AGalfra/ucos-II/scr/Micrium/Template/OS2/os_cfg.h

/*
*********************************************************************************************************
*                                                uC/OS-II
*                                          The Real-Time Kernel
*
*                         (c) Copyright 1992-2019; Silicon Laboratories Inc.,
*                                400 W. Cesar Chavez, Austin, TX 78701
*
*                   All rights reserved. Protected by international copyright laws.
*
*                  Your use of this software is subject to your acceptance of the terms
*                  of a Silicon Labs Micrium software license, which can be obtained by
*                  contacting info@micrium.com. If you do not agree to the terms of this
*                  license, you may not use this software.
*
*                  Please help us continue to provide the Embedded community with the finest
*                  software available. Your honesty is greatly appreciated.
*
*                    You can find our product's documentation at: doc.micrium.com
*
*                          For more information visit us at: www.micrium.com
*********************************************************************************************************
*/

/*
*********************************************************************************************************
*
*                                 uC/OS-II Configuration File for V2.9x
*
* Filename : os_cfg.h
* Version  : V2.92.16
*********************************************************************************************************
*/

#ifndef OS_CFG_H
#define OS_CFG_H


                                       /* ---------------------- MISCELLANEOUS ----------------------- */
#define OS_APP_HOOKS_EN           1u   /* Application-defined hooks are called from the uC/OS-II hooks */
#define OS_ARG_CHK_EN             1u   /* Enable (1) or Disable (0) argument checking                  */
#define OS_CPU_HOOKS_EN           1u   /* uC/OS-II hooks are found in the processor port files         */

#define OS_DEBUG_EN               0u   /* Enable(1) debug variables                                    */

#define OS_EVENT_MULTI_EN         1u   /* Include code for OSEventPendMulti()                          */
#define OS_EVENT_NAME_EN          1u   /* Enable names for Sem, Mutex, Mbox and Q                      */

#define OS_LOWEST_PRIO           63u   /* Defines the lowest priority that can be assigned ...         */
                                       /* ... MUST NEVER be higher than 254!                           */

#define OS_MAX_EVENTS            12u   /* Max. number of event control blocks in your application      */
#define OS_MAX_FLAGS              5u   /* Max. number of Event Flag Groups    in your application      */
#define OS_MAX_MEM_PART           5u   /* Max. number of memory partitions                             */
#define OS_MAX_QS                 4u   /* Max. number of queue control blocks in your application      */
#define OS_MAX_TASKS             20u   /* Max. number of tasks in your application, MUST be >= 2       */

#define OS_SCHED_LOCK_EN          1u   /* Include code for OSSchedLock() and OSSchedUnlock()           */

#define OS_TICK_STEP_EN           1u   /* Enable tick stepping feature for uC/OS-View                  */
#define OS_TICKS_PER_SEC       1000u   /* Set the number of ticks in one second                        */

#define OS_TLS_TBL_SIZE           0u   /* Size of Thread-Local Storage Table                           */


                                       /* --------------------- TASK STACK SIZE ---------------------- */
#define OS_TASK_TMR_STK_SIZE    128u   /* Timer      task stack size (# of OS_STK wide entries)        */
#define OS_TASK_STAT_STK_SIZE   128u   /* Statistics task stack size (# of OS_STK wide entries)        */
#define OS_TASK_IDLE_STK_SIZE   128u   /* Idle       task stack size (# of OS_STK wide entries)        */


                                       /* --------------------- TASK MANAGEMENT ---------------------- */
#define OS_TASK_CHANGE_PRIO_EN    1u   /*     Include code for OSTaskChangePrio()                      */
#define OS_TASK_CREATE_EN         1u   /*     Include code for OSTaskCreate()                          */
#define OS_TASK_CREATE_EXT_EN     1u   /*     Include code for OSTaskCreateExt()                       */
#define OS_TASK_DEL_EN            1u   /*     Include code for OSTaskDel()                             */
#define OS_TASK_NAME_EN           1u   /*     Enable task names                                        */
#define OS_TASK_PROFILE_EN        1u   /*     Include variables in OS_TCB for profiling                */
#define OS_TASK_QUERY_EN          1u   /*     Include code for OSTaskQuery()                           */
#define OS_TASK_REG_TBL_SIZE      1u   /*     Size of task variables array (#of INT32U entries)        */
#define OS_TASK_STAT_EN           1u   /*     Enable (1) or Disable(0) the statistics task             */
#define OS_TASK_STAT_STK_CHK_EN   1u   /*     Check task stacks from statistic task                    */
#define OS_TASK_SUSPEND_EN        1u   /*     Include code for OSTaskSuspend() and OSTaskResume()      */
#define OS_TASK_SW_HOOK_EN        1u   /*     Include code for OSTaskSwHook()                          */


                                       /* ----------------------- EVENT FLAGS ------------------------ */
#define OS_FLAG_EN                1u   /* Enable (1) or Disable (0) code generation for EVENT FLAGS    */
#define OS_FLAG_ACCEPT_EN         1u   /*     Include code for OSFlagAccept()                          */
#define OS_FLAG_DEL_EN            1u   /*     Include code for OSFlagDel()                             */
#define OS_FLAG_NAME_EN           1u   /*     Enable names for event flag group                        */
#define OS_FLAG_QUERY_EN          1u   /*     Include code for OSFlagQuery()                           */
#define OS_FLAG_WAIT_CLR_EN       1u   /* Include code for Wait on Clear EVENT FLAGS                   */
#define OS_FLAGS_NBITS           16u   /* Size in #bits of OS_FLAGS data type (8, 16 or 32)            */


                                       /* -------------------- MESSAGE MAILBOXES --------------------- */
#define OS_MBOX_EN                1u   /* Enable (1) or Disable (0) code generation for MAILBOXES      */
#define OS_MBOX_ACCEPT_EN         1u   /*     Include code for OSMboxAccept()                          */
#define OS_MBOX_DEL_EN            1u   /*     Include code for OSMboxDel()                             */
#define OS_MBOX_PEND_ABORT_EN     1u   /*     Include code for OSMboxPendAbort()                       */
#define OS_MBOX_POST_EN           1u   /*     Include code for OSMboxPost()                            */
#define OS_MBOX_POST_OPT_EN       1u   /*     Include code for OSMboxPostOpt()                         */
#define OS_MBOX_QUERY_EN          1u   /*     Include code for OSMboxQuery()                           */


                                       /* --------------------- MEMORY MANAGEMENT -------------------- */
#define OS_MEM_EN                 1u   /* Enable (1) or Disable (0) code generation for MEMORY MANAGER */
#define OS_MEM_NAME_EN            1u   /*     Enable memory partition names                            */
#define OS_MEM_QUERY_EN           1u   /*     Include code for OSMemQuery()                            */


                                       /* ---------------- MUTUAL EXCLUSION SEMAPHORES --------------- */
#define OS_MUTEX_EN               1u   /* Enable (1) or Disable (0) code generation for MUTEX          */
#define OS_MUTEX_ACCEPT_EN        1u   /*     Include code for OSMutexAccept()                         */
#define OS_MUTEX_DEL_EN           1u   /*     Include code for OSMutexDel()                            */
#define OS_MUTEX_QUERY_EN         1u   /*     Include code for OSMutexQuery()                          */


                                       /* ---------------------- MESSAGE QUEUES ---------------------- */
#define OS_Q_EN                   1u   /* Enable (1) or Disable (0) code generation for QUEUES         */
#define OS_Q_ACCEPT_EN            1u   /*     Include code for OSQAccept()                             */
#define OS_Q_DEL_EN               1u   /*     Include code for OSQDel()                                */
#define OS_Q_FLUSH_EN             1u   /*     Include code for OSQFlush()                              */
#define OS_Q_PEND_ABORT_EN        1u   /*     Include code for OSQPendAbort()                          */
#define OS_Q_POST_EN              1u   /*     Include code for OSQPost()                               */
#define OS_Q_POST_FRONT_EN        1u   /*     Include code for OSQPostFront()                          */
#define OS_Q_POST_OPT_EN          1u   /*     Include code for OSQPostOpt()                            */
#define OS_Q_QUERY_EN             1u   /*     Include code for OSQQuery()                              */


                                       /* ------------------------ SEMAPHORES ------------------------ */
#define OS_SEM_EN                 1u   /* Enable (1) or Disable (0) code generation for SEMAPHORES     */
#define OS_SEM_ACCEPT_EN          1u   /*    Include code for OSSemAccept()                            */
#define OS_SEM_DEL_EN             1u   /*    Include code for OSSemDel()                               */
#define OS_SEM_PEND_ABORT_EN      1u   /*    Include code for OSSemPendAbort()                         */
#define OS_SEM_QUERY_EN           1u   /*    Include code for OSSemQuery()                             */
#define OS_SEM_SET_EN             1u   /*    Include code for OSSemSet()                               */


                                       /* --------------------- TIME MANAGEMENT ---------------------- */
#define OS_TIME_DLY_HMSM_EN       1u   /*     Include code for OSTimeDlyHMSM()                         */
#define OS_TIME_DLY_RESUME_EN     1u   /*     Include code for OSTimeDlyResume()                       */
#define OS_TIME_GET_SET_EN        1u   /*     Include code for OSTimeGet() and OSTimeSet()             */
#define OS_TIME_TICK_HOOK_EN      1u   /*     Include code for OSTimeTickHook()                        */


                                       /* --------------------- TIMER MANAGEMENT --------------------- */
#define OS_TMR_EN                 1u   /* Enable (1) or Disable (0) code generation for TIMERS         */
#define OS_TMR_CFG_MAX           16u   /*     Maximum number of timers                                 */
#define OS_TMR_CFG_NAME_EN        1u   /*     Determine timer names                                    */
#define OS_TMR_CFG_WHEEL_SIZE     7u   /*     Size of timer wheel (#Spokes)                            */
#define OS_TMR_CFG_TICKS_PER_SEC 10u   /*     Rate at which timer management task runs (Hz)            */


                                       /* ---------------------- TRACE RECORDER ---------------------- */
#define OS_TRACE_EN               0u   /* Enable (1) or Disable (0) uC/OS-II Trace instrumentation     */
#define OS_TRACE_API_ENTER_EN     0u   /* Enable (1) or Disable (0) uC/OS-II Trace API enter instrum.  */
#define OS_TRACE_API_EXIT_EN      0u   /* Enable (1) or Disable (0) uC/OS-II Trace API exit  instrum.  */

#endif
