AGalfra/ucos-II/scr/Core/Src/bitmap.h

/*
unsigned char logo[] = {
0x00, 0x00, 0x00, 0x00, 0x0F, 0xF8, 0x00, 0x00, 0x00, 0x00, 0x00, 0x00, 0x3F, 0xFF, 0x00, 0x00,
0x00, 0x00, 0x00, 0x00, 0xFF, 0xFF, 0x80, 0x00, 0x00, 0x00, 0x00, 0x01, 0xFF, 0xFF, 0xE0, 0x00,
0x00, 0x00, 0x00, 0x07, 0xFF, 0xFF, 0xF8, 0x00, 0x00, 0x00, 0x00, 0x0F, 0xE0, 0x0F, 0xF8, 0x00,
0x00, 0x00, 0x00, 0x1F, 0xC0, 0x07, 0xFC, 0x00, 0x00, 0x00, 0x00, 0x1F, 0x80, 0x03, 0xFE, 0x00,
0x00, 0x00, 0x00, 0x3F, 0x8F, 0xFF, 0xFF, 0x00, 0x00, 0x00, 0x00, 0x7F, 0x1F, 0xFF, 0xFF, 0x80,
0x00, 0x00, 0x00, 0x7F, 0x3F, 0xFF, 0xFF, 0x80, 0x00, 0x00, 0x00, 0xFE, 0x7F, 0xFF, 0xFF, 0x80,
0x00, 0x00, 0x00, 0xFE, 0xFF, 0xFF, 0xFF, 0x80, 0x00, 0x00, 0x01, 0xFE, 0xFF, 0xFF, 0xFF, 0xC0,
0x00, 0x00, 0x01, 0xFF, 0xFF, 0xFF, 0xFF, 0xC0, 0x00, 0x00, 0x03, 0xFF, 0xFF, 0xFF, 0xFF, 0xC0,
0x00, 0x00, 0x07, 0xFF, 0xFF, 0xFF, 0xFF, 0xC0, 0x00, 0x00, 0x07, 0xFF, 0xFF, 0xFF, 0xFF, 0xC0,
0x00, 0x00, 0x0F, 0xFF, 0xFF, 0xFF, 0xFF, 0xC0, 0x00, 0x00, 0x0F, 0xFF, 0xFF, 0xFF, 0xFF, 0xC0,
0x00, 0x00, 0x1F, 0xFF, 0xFF, 0xFF, 0xFF, 0xC0, 0x00, 0x00, 0x1F, 0xFF, 0xFF, 0xFF, 0xFF, 0xC0,
0x00, 0x00, 0x3F, 0xFF, 0xFF, 0xFF, 0xFF, 0x80, 0x00, 0x00, 0x7F, 0xFF, 0xFF, 0xFF, 0xFF, 0x80,
0x00, 0x00, 0xFF, 0xFF, 0xFF, 0xFF, 0xFF, 0x80, 0x00, 0x00, 0xFF, 0xFF, 0xFF, 0xFF, 0xFF, 0x80,
0x00, 0x00, 0xFF, 0xFF, 0xFF, 0xFF, 0xFF, 0x00, 0x00, 0x01, 0xFD, 0xFF, 0xFF, 0xFF, 0xFE, 0x00,
0x00, 0x03, 0xF8, 0x7F, 0xFF, 0xFF, 0xFE, 0x00, 0x00, 0x03, 0xF8, 0x1F, 0xFF, 0xFF, 0xFC, 0x00,
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
0x00, 0x07, 0x81, 0xC0, 0xF0, 0x00, 0x0C, 0x63, 0x40, 0x00, 0x00, 0x00, 0x00, 0x00, 0x00, 0x00,
0x00, 0x07, 0x03, 0xE0, 0x78, 0x00, 0x0E, 0x63, 0xC0, 0x00, 0x00, 0x00, 0x00, 0x00, 0x00, 0x00,
0x00, 0x0E, 0x0F, 0xF8, 0x38, 0x00, 0x07, 0xC1, 0x80, 0x00, 0x00, 0x00, 0x00, 0x00, 0x00, 0x00,
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
};
